goebish/triversity-multipath-erazer/MultipathErazer/logo.h

// bottom to top 160*128 RLE bitmap
// for compression algorithm
// see https://msdn.microsoft.com/en-us/library/windows/desktop/dd183383

const uint8_t splash_logo[] PROGMEM = {
     0x35,0xff,0x00,0x0f,0xf7,0xdf,0xbd,0x96,0x88,0x77,0x6c
    ,0x64,0x71,0x7b,0x8a,0x9a,0xc7,0xe5,0xfc,0x00,0x5c,0xff,0x00,0x00,0x32,0xff,0x00,0x08,0xf9,0xd0,0x95,0x5b,0x2d,0x20,0x1b,0x16,0x05,0x14,0x00,0x07,0x17,0x1f,0x25
    ,0x3a,0x6b,0x9f,0xd8,0x00,0x5a,0xff,0x00,0x00,0x30,0xff,0x00,0x19,0xf6,0xb9,0x62,0x25,0x18,0x16,0x1c,0x21,0x2b,0x33,0x3a,0x3f,0x41,0x3d,0x38,0x2e,0x25,0x1b,0x15
    ,0x15,0x1e,0x33,0x77,0xc5,0xfd,0x00,0x57,0xff,0x00,0x00,0x2e,0xff,0x00,0x1c,0xfb,0xc1,0x59,0x1e,0x19,0x1f,0x2b,0x3a,0x4b,0x5d,0x60,0x72,0x7d,0x80,0x7f,0x86,0x81
    ,0x78,0x72,0x65,0x4d,0x36,0x21,0x16,0x17,0x28,0x73,0xcc,0x56,0xff,0x00,0x00,0x2d,0xff,0x00,0x1f,0xe3,0x78,0x1f,0x18,0x23,0x33,0x46,0x55,0x78,0x9b,0xbc,0xe4,0xe0
    ,0xec,0xf2,0xf3,0xef,0xe5,0xdc,0xd1,0xaf,0xa0,0x81,0x6e,0x49,0x29,0x17,0x15,0x32,0x95,0xf3,0x00,0x54,0xff,0x00,0x00,0x2c,0xff,0x00,0x0a,0xcc,0x38,0x18,0x23,0x31
    ,0x43,0x58,0x8b,0xd7,0xf3,0x0c,0xff,0x00,0x0b,0xfd,0xdb,0xb9,0x98,0x7b,0x4e,0x26,0x15,0x1b,0x64,0xd2,0x00,0x53,0xff,0x00,0x00,0x2a,0xff,0x00,0x09,0xfc,0xa7,0x20
    ,0x1c,0x2b,0x38,0x49,0x9a,0xe5,0x00,0x12,0xff,0x00,0x09,0xf3,0xb6,0x92,0x75,0x3a,0x1c,0x14,0x42,0xc3,0x00,0x52,0xff,0x00,0x00,0x29,0xff,0x00,0x08,0xfc,0x96,0x1a
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
    ,0x36,0xff,0xf7,0xf8,0xf8,0xf8,0xf7,0xfb,0xfa,0xf6,0xfa,0xf5,0xf5,0xf6,0xfa,0xf7,0xf9,0xf7,0xf5,0xf6,0xf8,0xf9,0xf8,0xf8,0xf5,0xf6,0xf9,0xf7,0xf8,0xf8,0xf5,0xf5
    ,0xfa,0xf8,0xf9,0xeb,0x65,0x31,0x1d,0xa3,0xf9,0xfe,0xfa,0xf6,0xfa,0xc0,0x3a,0x28,0x26,0x26,0x27,0x27,0x26,0x27,0x27,0x04,0x26,0x00,0x12,0x27,0x28,0x28,0x28,0x24
    ,0x1d,0x23,0x27,0x26,0x26,0x27,0x28,0x28,0x27,0x26,0x26,0x19,0x8d,0x05,0xf8,0x00,0x4f,0xe8,0x78,0x34,0x1a,0x97,0xf7,0xfb,0xfd,0xf5,0xf0,0xf3,0xfb,0xf9,0xfa,0xf7
    ,0xf8,0xf7,0xfa,0xf6,0xfa,0xf5,0xf7,0xfa,0xf7,0xf8,0xf5,0xf6,0xfe,0xfa,0xf3,0xf1,0xf5,0xfb,0xf5,0xf7,0xfe,0xf8,0xf2,0xf3,0xfc,0xfa,0xf6,0xf5,0xfa,0xf8,0xf7,0xf8
    ,0xf8,0xf7,0xfb,0xf9,0xf7,0xfa,0xf4,0xf5,0xf9,0xfa,0xf6,0xf8,0xf9,0xf7,0xf9,0xf7,0xfa,0xf8,0xf9,0xf8,0xf5,0xfb,0xf7,0xf7,0xf9,0xfa,0xf8,0xf8,0xf8,0xf7,0xfa,0xff
    ,0x00,0x00,0x00,0x00,0x9a,0xb4,0x85,0x84,0x84,0x84,0x82,0x8d,0x8b,0x82,0xa4,0xff,0xff,0xff,0xa5,0x82,0x85,0xf9,0xff,0xff,0xe3,0x88,0x80,0xc1,0xff,0xff,0xaf,0x84
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
};
